Samuel-Malaj/PicoCalc-Open-Source-Student-Scientific-Calculator/Software/utils.py

import lowpower
import time
import machine
from machine import Pin
from icons import *
from inputs import *
from WiFi import *
from OLED import *

def power_off():
    safety_pin = machine.Pin(1, machine.Pin.IN, machine.Pin.PULL_UP)
    if safety_pin.value() == 0:
        print("Safety mode: Sleep disabled. Connect GP1 to 3V3 to allow sleep.")
        while True: time.sleep(1)

    button = machine.Pin(0, machine.Pin.IN, machine.Pin.PULL_UP)
    indicator = machine.Pin(7, machine.Pin.OUT, value=0)

    LED = Pin('LED', Pin.OUT)
    LED.value(1)
    LED.value(0)
    lowpower.dormant_until_pin(0)
    
def main_menu():
    y = 0
    clear_all()
    modes = ['calc mode', 'notepad mode', 'sms mode', 'WiFi', 'whatsapp', 'games', 'weather']
    while True:
        clear_main()
        oled.rect(0, 0, 128, 10, 0, fill=True)
        add_icon(oled, NUMERICAL, 95, 0)
        indicate_wifi()
        oled.blit(calc_icon, 0, 10+y)
        oled.blit(notepad_icon, 63, 10+y)
        oled.blit(sms_icon, 0, 38+y)
        oled.blit(wifi_icon, 63, 38+y)
        oled.blit(whatsapp_icon, 0, 66+y)
        oled.blit(games_icon, 63, 66+y)
        oled.blit(weather_icon, 0, 94+y)
        oled.show()
        
        X, Y = listen()
        button = menu_array[Y][X]
        print(button)
        
        if button.isdigit():
            selected = int(button)
            if selected <= len(modes) and selected > 0:
                return modes[int(button)-1]

        elif button == 'DOWN':
            clear_main()
            y -= 15
            
        elif button == 'UP':
            clear_main()
            y += 15
